Lamprichauns/lamp-os/hardware/build/images/photo_2025-04-13_17-59-18.jpg

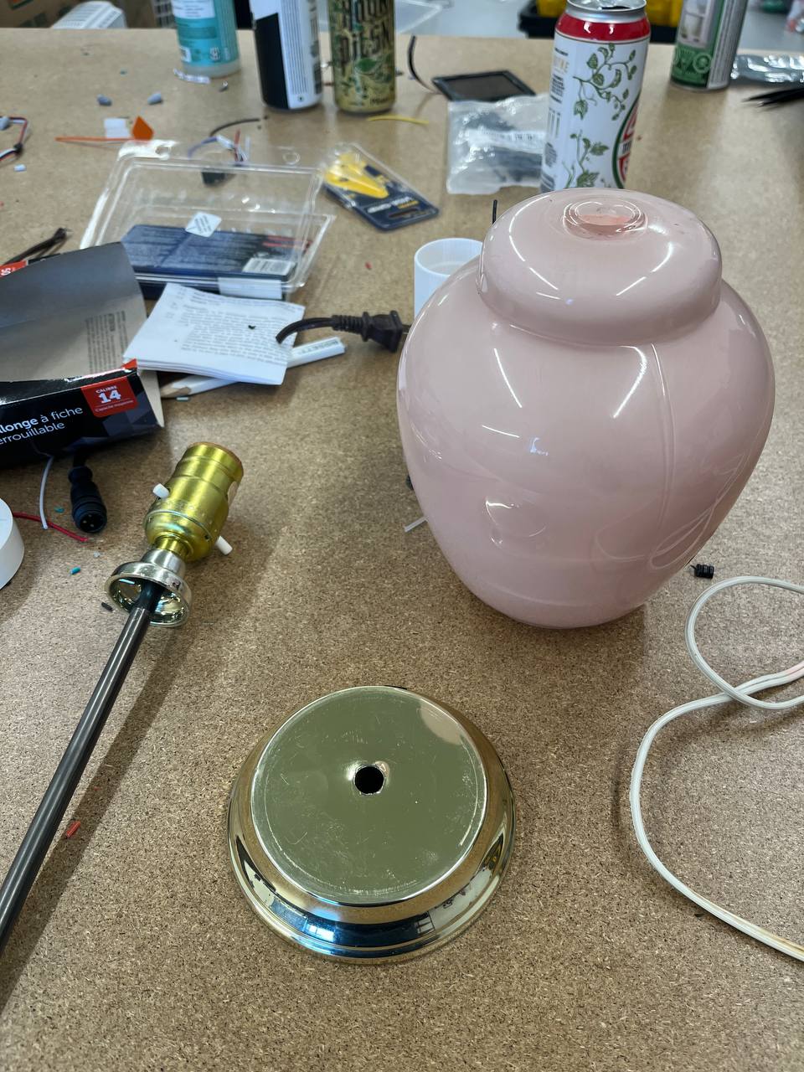
hardware/build/images/photo_2025-04-13_17-59-18.jpg
