Lamprichauns/lamp-os/software/lamp-os/src/core/frame_buffer.hpp

#ifndef LAMP_CORE_FRAME_BUFFER_H
#define LAMP_CORE_FRAME_BUFFER_H

#include <Adafruit_NeoPixel.h>
#include <Arduino.h>

#include <vector>

#include "./util/color.hpp"

namespace lamp {
/**
 * @brief the frame buffer holds a copy of the current scene's pixel
 * colors for all layered draw operations
 */
class FrameBuffer {
 private:
  uint8_t i = 0;

 public:
  std::vector<Color> defaultColors;
  std::vector<Color> previousBuffer;
  uint8_t pixelCount = 0;
  Adafruit_NeoPixel *driver = nullptr;
  std::vector<Color> buffer;

  FrameBuffer();

  /**
   * @brief Setup initializer
   * @param [in] inDefaultColors The user's default lamp colors {Color, ..., n} n <= 50
   * @param [in] inPixelCount the number of neopixels in use
   * @param [in] inDriver the NeoPixel instance to use
   */
  void begin(std::vector<Color> inDefaultColors, uint8_t inPixelCount, Adafruit_NeoPixel *inDriver);

  /**
   * @brief fill the framebuffer with a single color
   */
  void fill(Color inColor);

  /**
   * @brief send values from buffer to the LED driver
   */
  void flush();
};
}  // namespace lamp
#endif
