Lamprichauns/lamp-os/software/artnet-repeater/src/secrets_sample.hpp

#ifndef SECRETS_H
#define SECRETS_H

// bluetooth advertising name: should be under 12 chars and lower case
#define SECRET_COORDINATOR_STAGE_NAME "lowercasename"

// wifi password and ssid combined can only be 24 chars total
#define SECRET_COORDINATOR_SSID "My SSID"
#define SECRET_COORDINATOR_PASSWORD "My Password"

#endif
